Orotavia/deej_controller/Software/tiny_clk_setup.h

/*
 * tiny_clk_setup.h
 *
 * Created: 4/7/2020 7:27:26 PM
 *  Author: stomp
 */ 
#include <avr/io.h>

#ifndef TINY_CLK_SETUP_H_
#define TINY_CLK_SETUP_H_

void clock_setup(uint8_t div);



#endif /* TINY_CLK_SETUP_H_ */
